OLIMEX/SOM/RK3188/RK3188-EVB/RK3188-EVB_Rev_C1.pdf

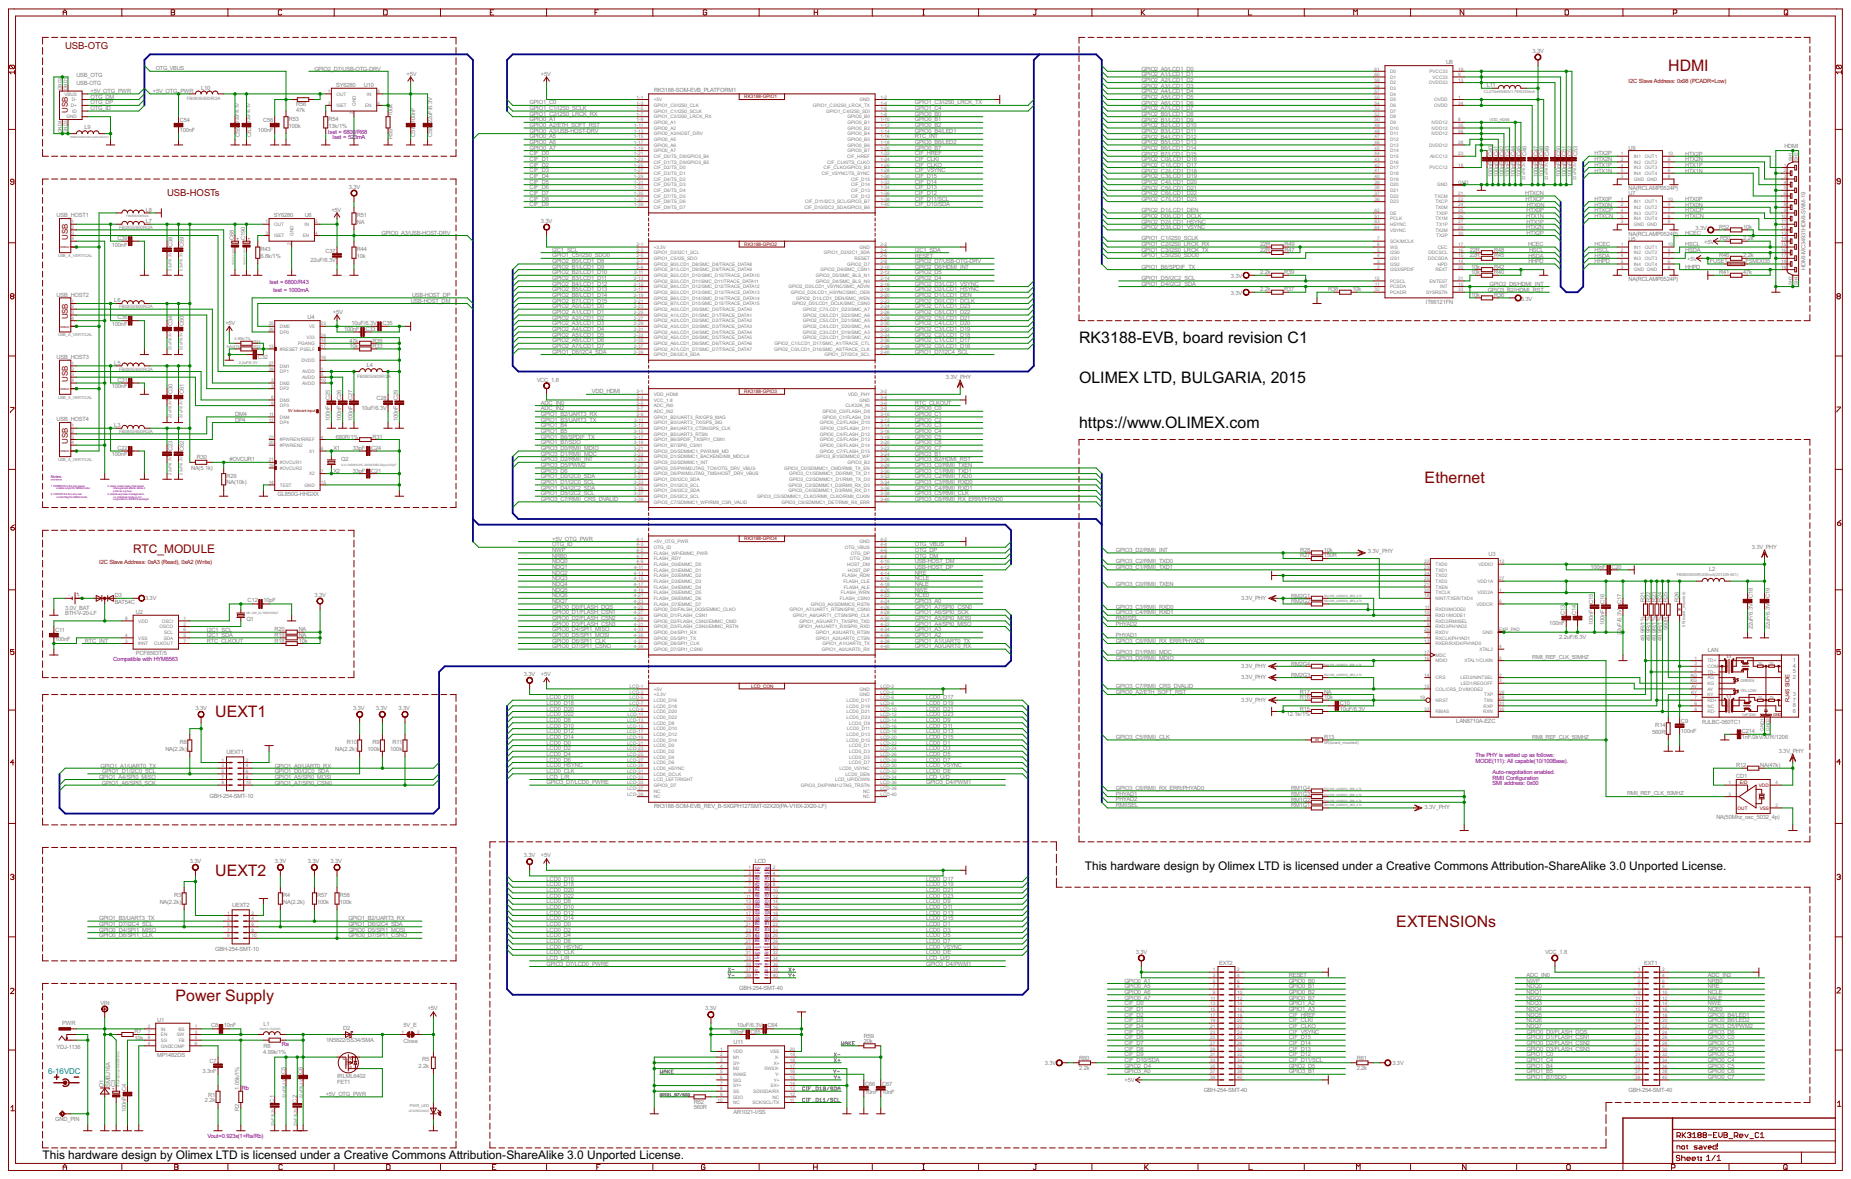
[picture p11: page 1]

I2C Slave Address: 0x98 (PCADR=Low)

NA(2 0uF/6.3V/tant)

RK3188-EVB, board revision C1 OLIMEX LTD, BULGARIA, 2015

https://www.OLIMEX.com

enable output forGANGmode; 1. PWREN1# is the onlypower- Notes:

i.e. individual mode is not supported on SSOP28 package!

I2C Slave Address: 0xA3 (Read), 0xA2 (Write)

The PHY is setted up as follows: MODE(111): All capable(10/100Base). Auto-negotiation enabled. RMII Configuration SMI address: 0x00

This hardware design by Olimex LTD is licensed under a Creative Commons Attribution-ShareAlike 3.0 Unported License.

GND_PIN
Vout=0.923x(1+Ra/Rb) This hardware design by Olimex LTD is licensed under a Creative Commons Attribution-ShareAlike 3.0 Unported License.
