OLIMEX/SOM/RK3188/RK3188-EVB/RK3188-EVB_Rev_C.pdf

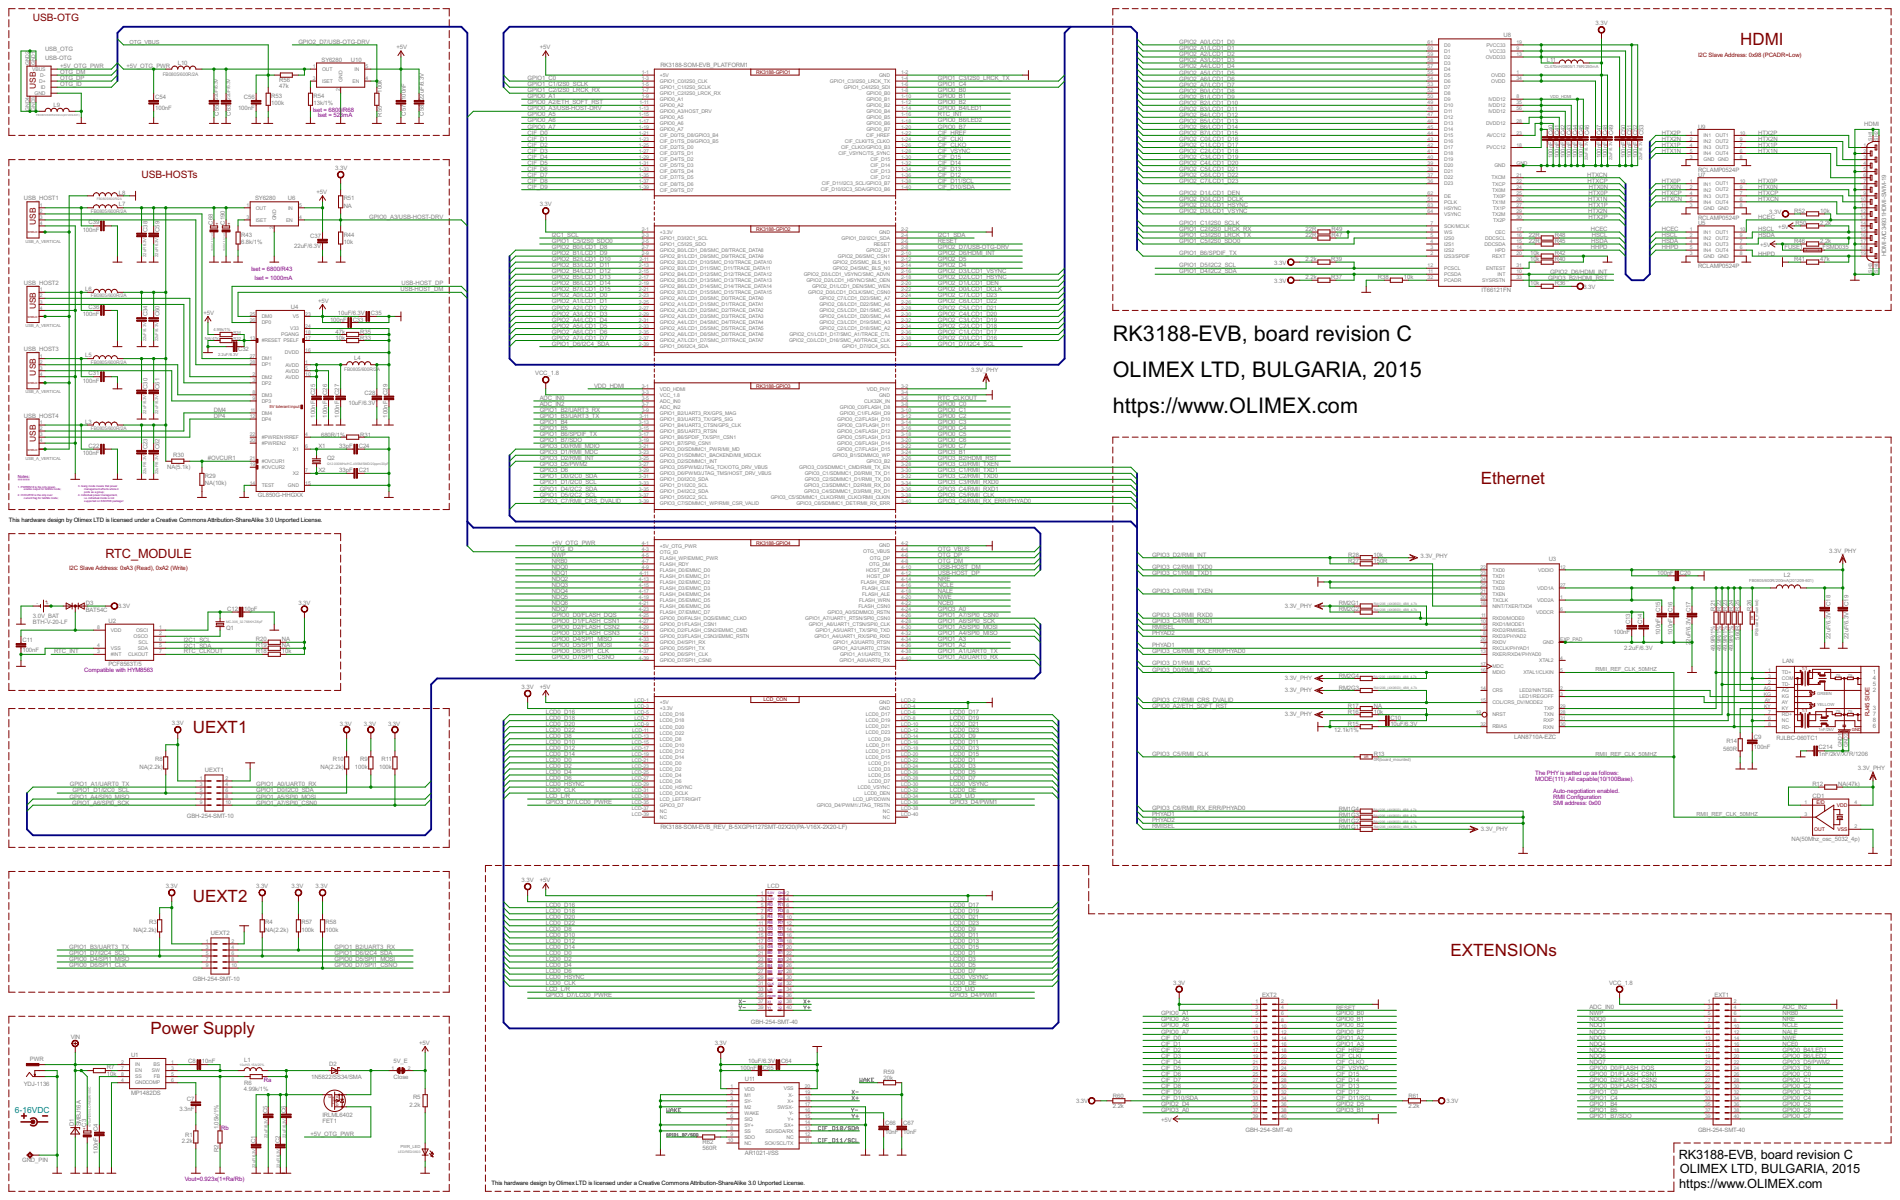
[picture p12: page 1]

I2C Slave Address: 0x98 (PCADR=Low)

NA(220uF/6.3V/tant)

https://www.OLIMEX.com

enable output for GANG mode; 1. PWREN1# is the only power- Notes:

i.e. individual mode is not supported on SSOP28 package!

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

I2C Slave Address: 0xA3 (Read), 0xA2 (Write)

USB-HOST_DP NRE NCLE NALE NWE NCE0 GPIO3_A0 GPIO1_A7/SPI0_CSN0 | GPIO3_C1/RMII_TXD1 GPIO3_C0/RMII_TXEN | 100nF | C20

KY 3 AG KG | COM NC AG KG AY KY | GREEN YELLOW

LCD0_D10 LCD-15 LCD0_D12 LCD-17 | LCD-16 LCD0_D11 LCD-18 LCD0_D13

LCD0_D2 LCD-23 LCD0_D4 LCD-25 | LCD-24 LCD0_D3 LCD-26 LCD0_D5

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

LCD0_D18 LCD0_D20 | 7 9 | 8 LCD0_D19 10 LCD0_D21

LCD0_D10 15 | 16 LCD0_D11

LCD0_D4 25 LCD0_D6 27 | 26 LCD0_D5 28 LCD0_D7

LCD0_HSYNC 29 LCD0_CLK 31 | HSYNC VSYNC CLK DE | 30 LCD0_VSYNC 32 LCD0_DE

GBH-254-SMT-40
RK3188-EVB, board revision C OLIMEX LTD, BULGARIA, 2015
