OLIMEX/SOM/A13/A13-SOM-LTE/A13-SOM-LTE_Rev_B.pdf

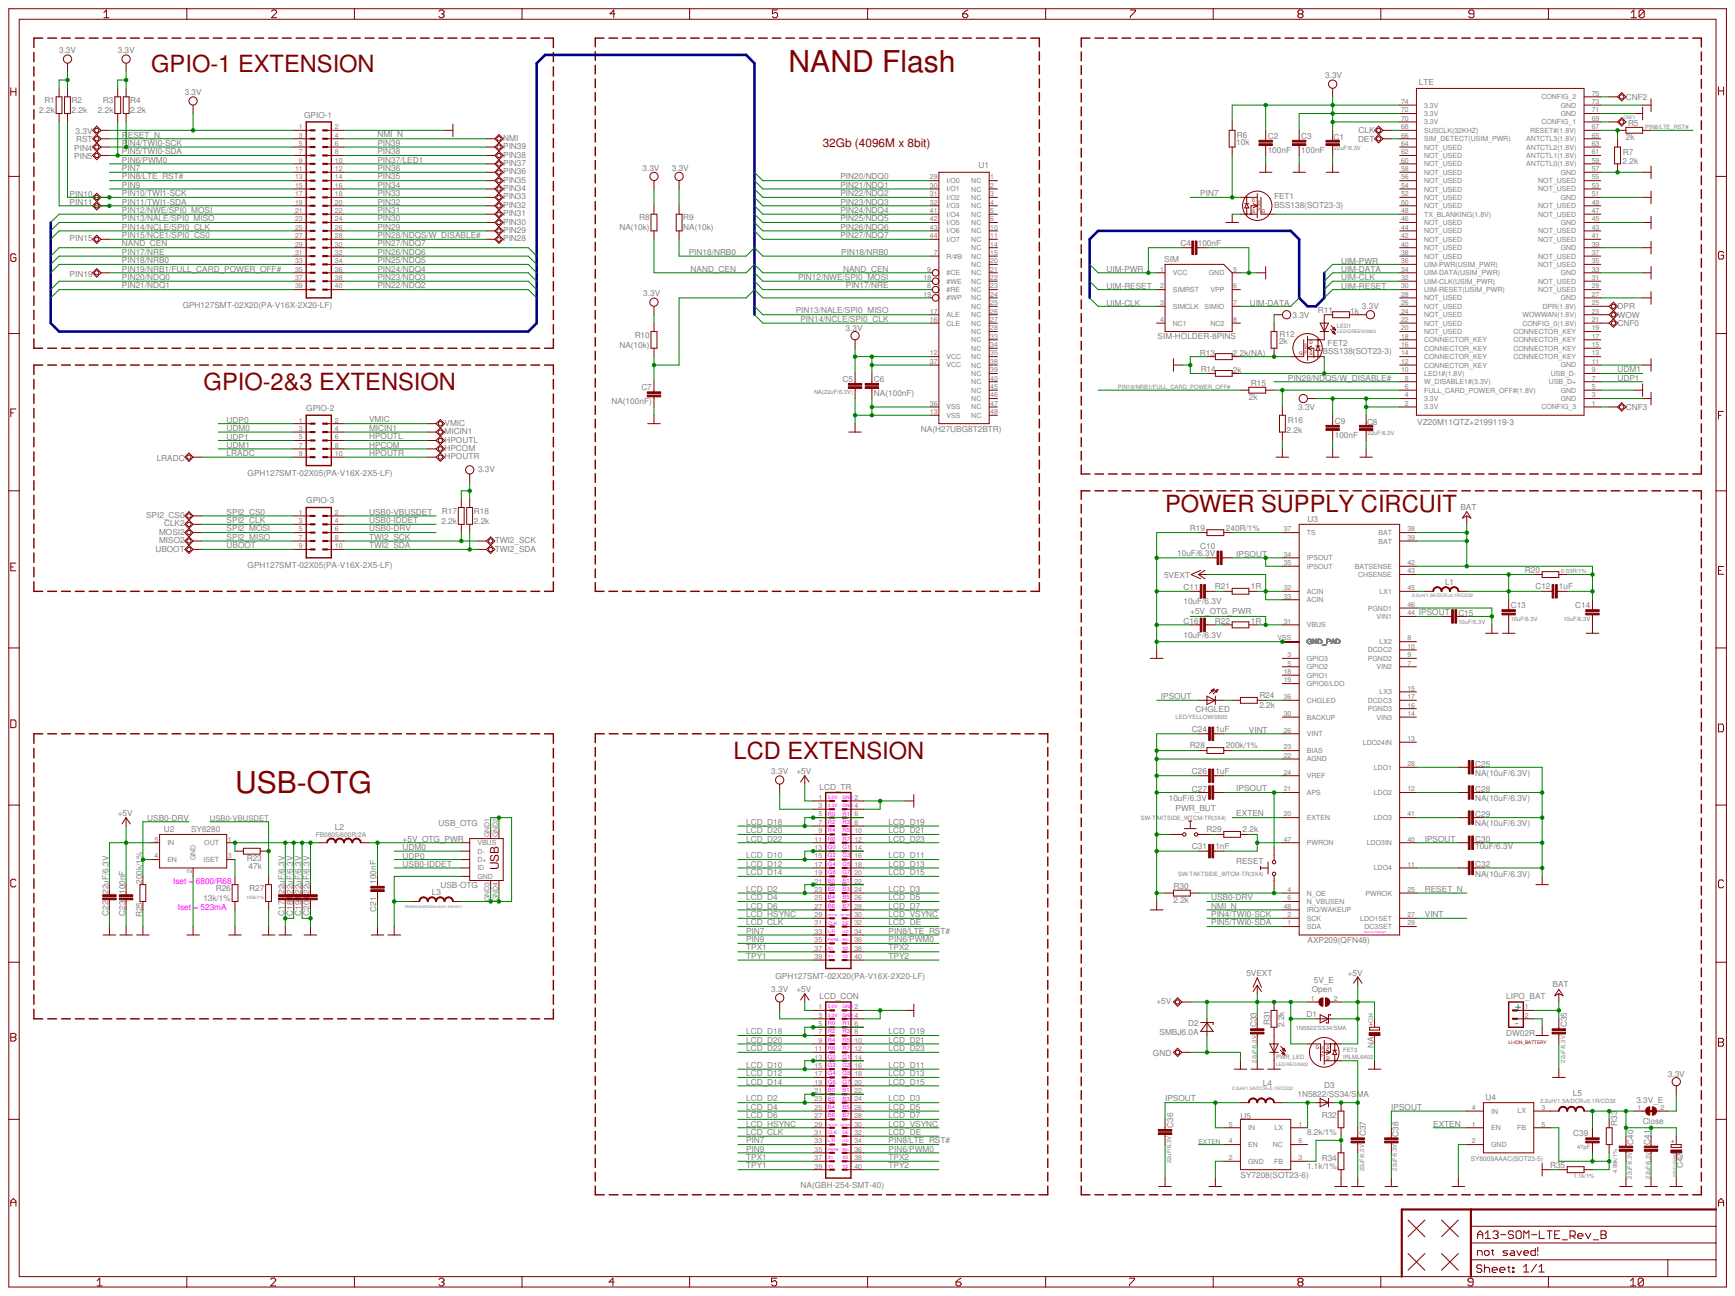
[picture p14: page 1]

PIN4/TWI0-SCK 5 | 6 PIN39 PIN38
