OLIMEX/SOM/A13/A13-SOM-WIFI/A13-SOM-WIFI_Rev_B.pdf

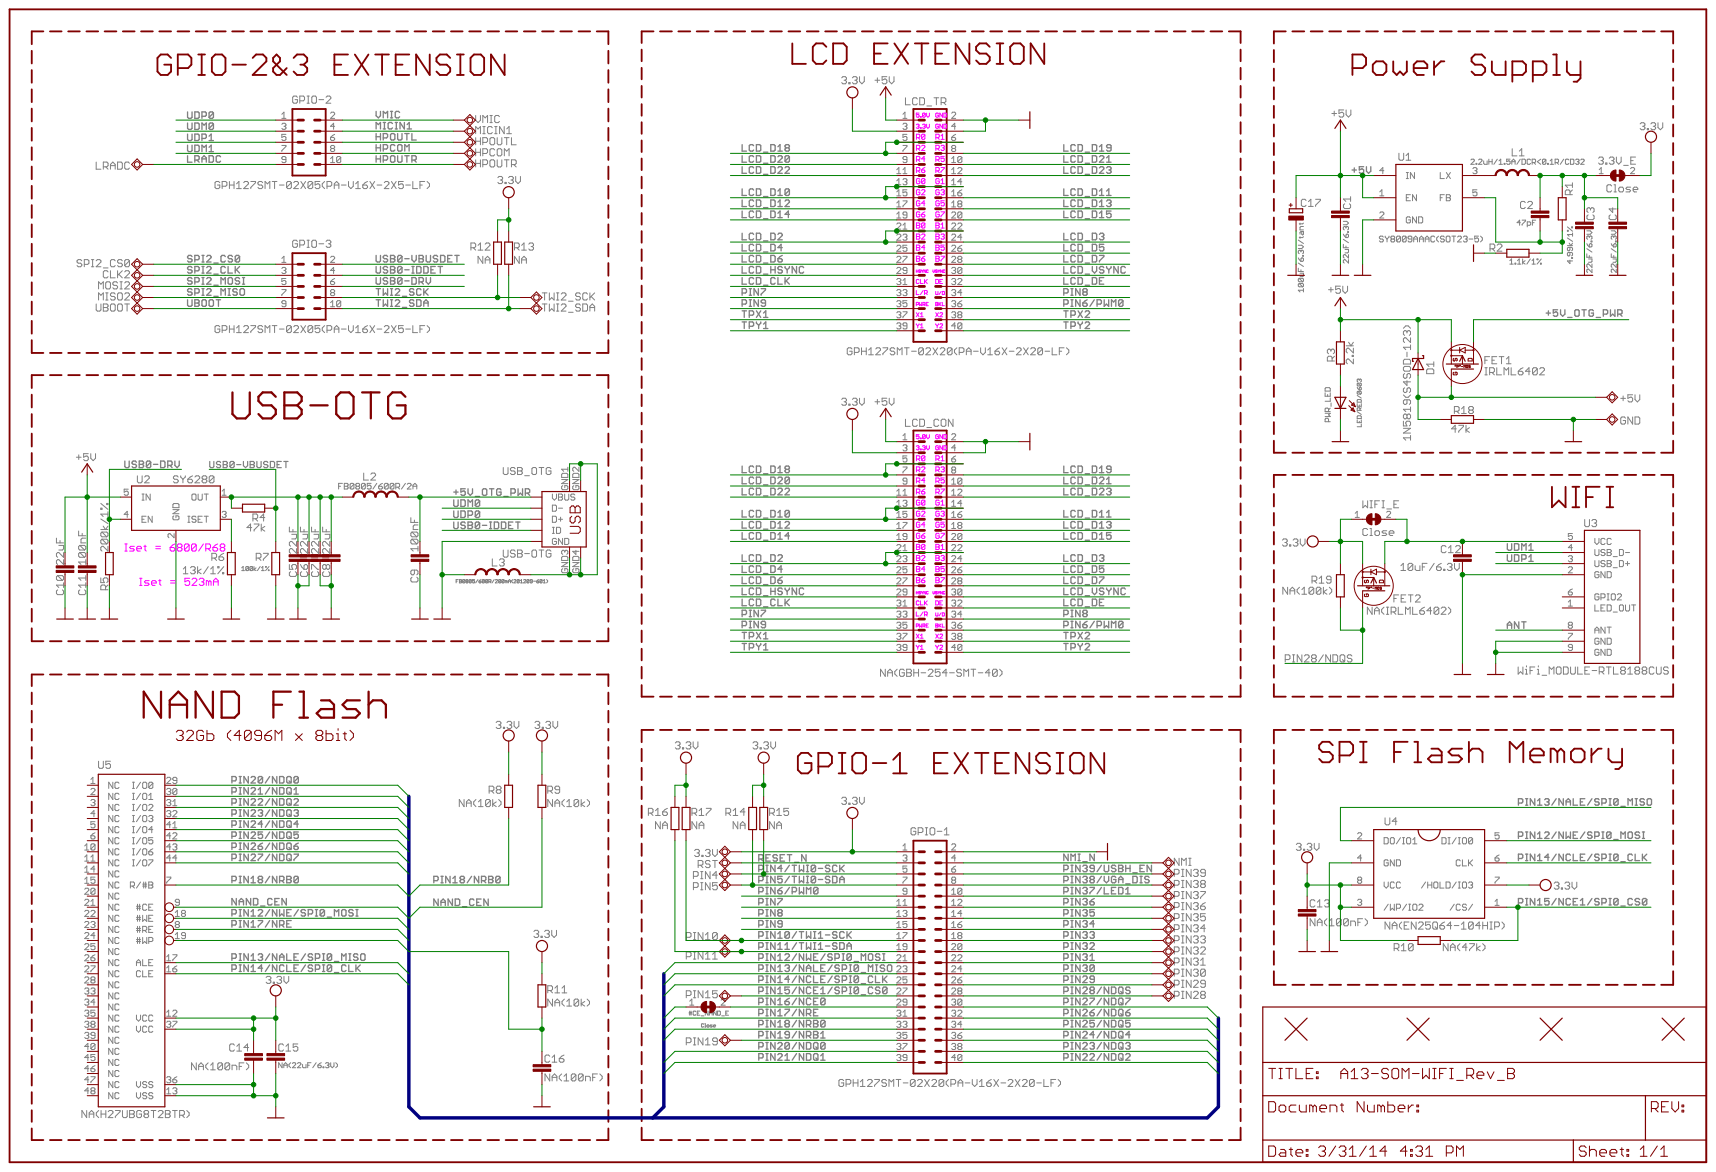
[picture p15: page 1]
