OLIMEX/SOM/A20/A20-SOM-EVB/A20-SOM-EVB_Rev_B.pdf

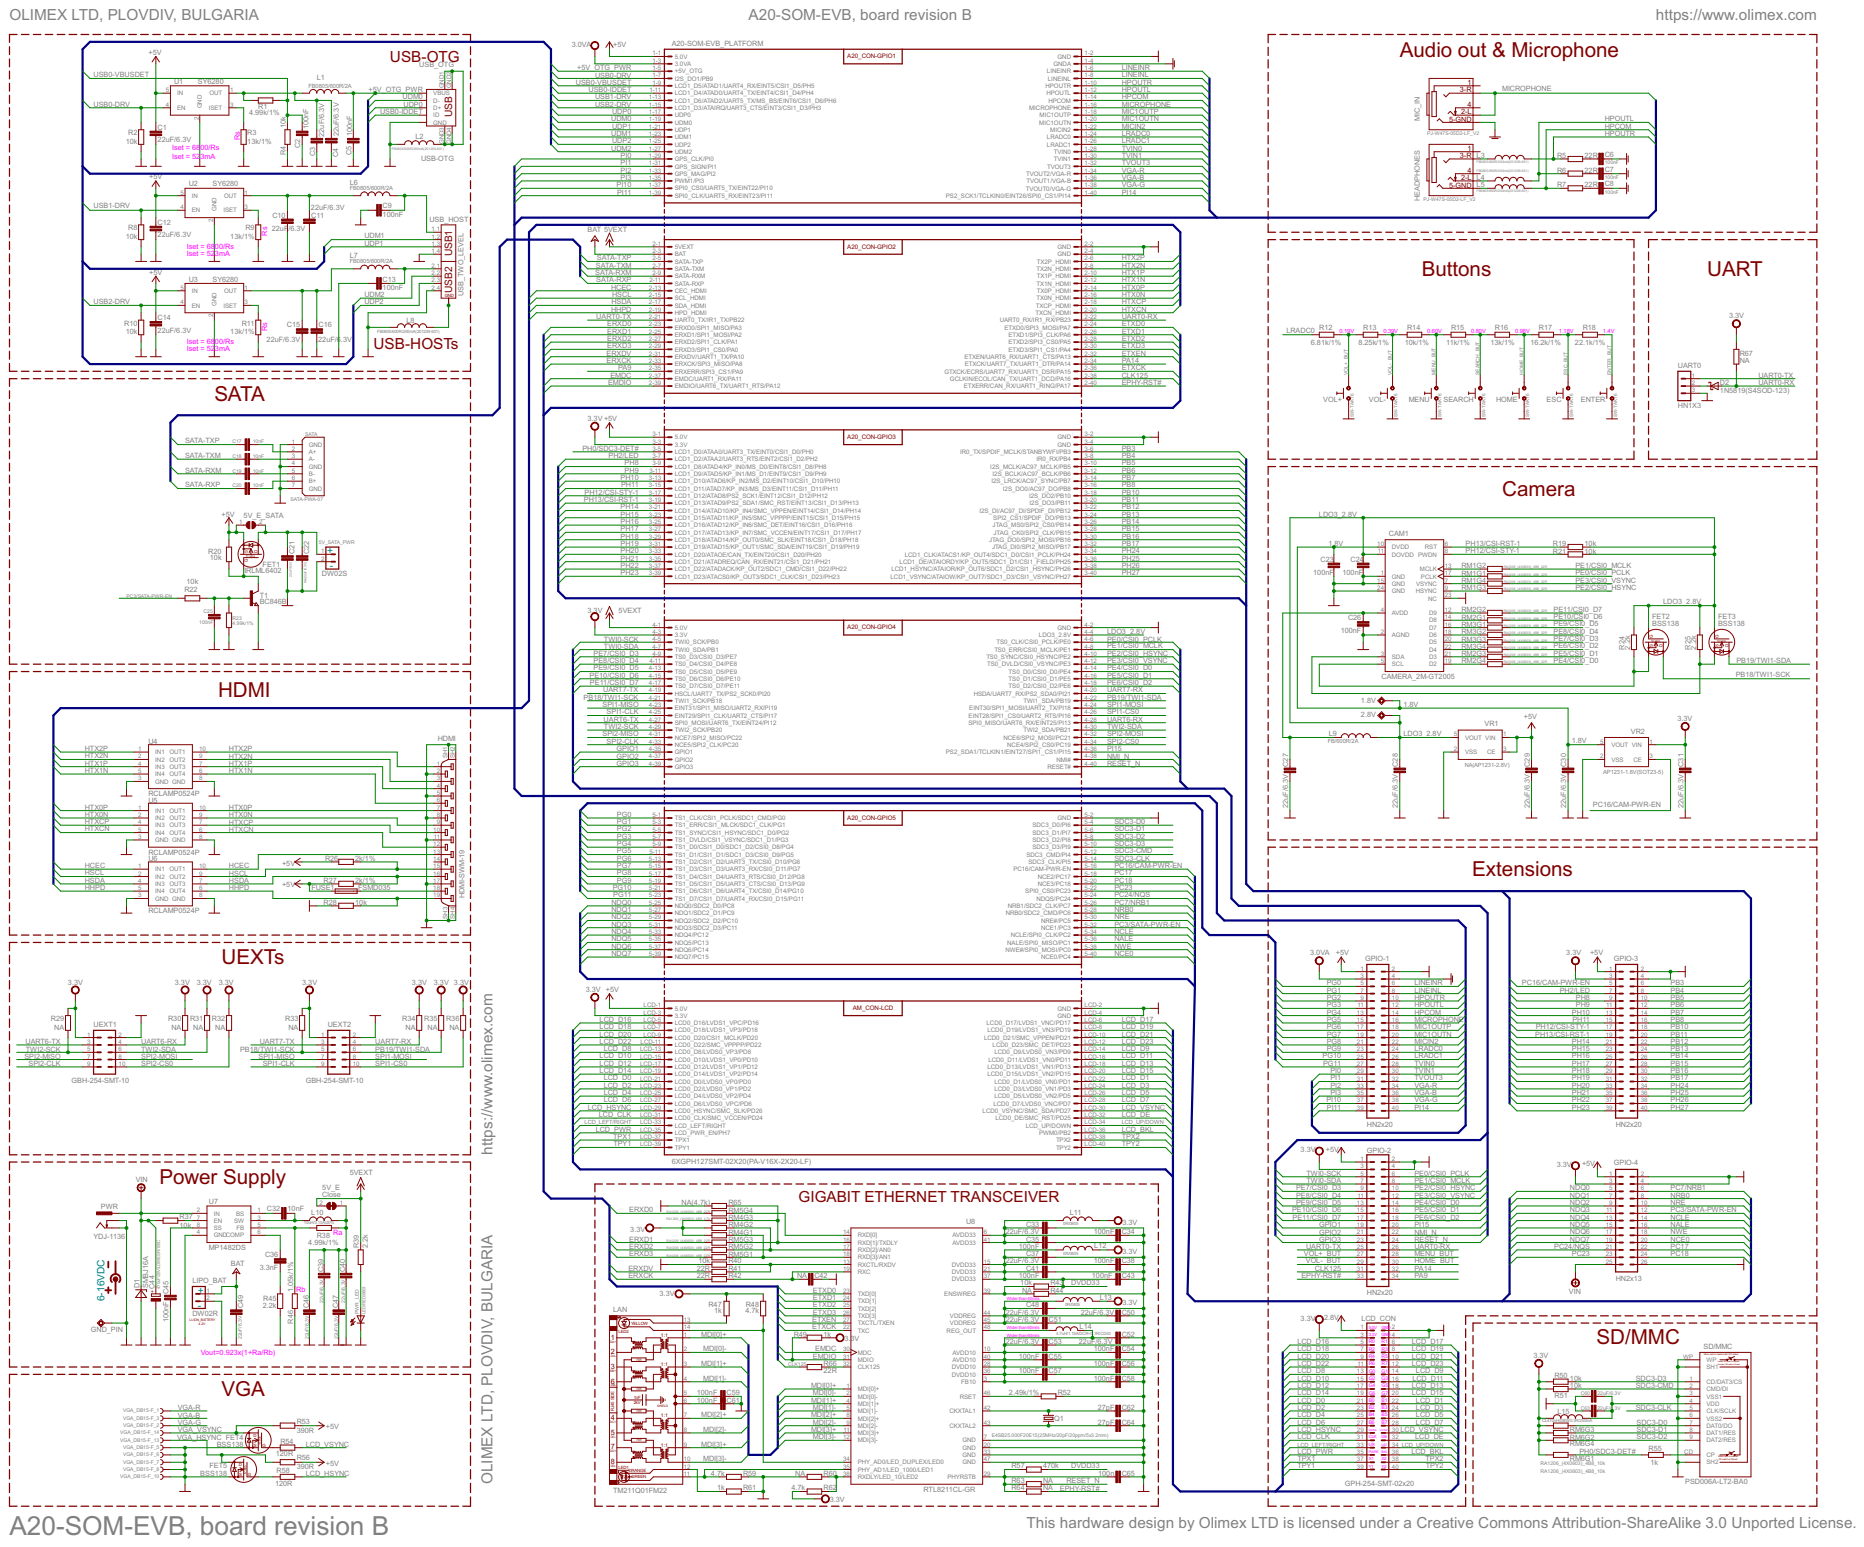
[picture p16: page 1]

OLIMEX LTD, PLOVDIV, BULGARIA

A20-SOM-EVB, board revision B

https://www.olimex.com

https:/ www.olimex.com

Wider than 40mils Wider than 60mils Wider than 60mils

When card is inserted with WP status: Locked, WP switch isOpened Unlocked, WP switch isClosed

When card is inserted, CP switch is Closed
