OLIMEX/SOM/A20/A20-SOM-EVB/A20-SOM-EVB_Rev_C.pdf

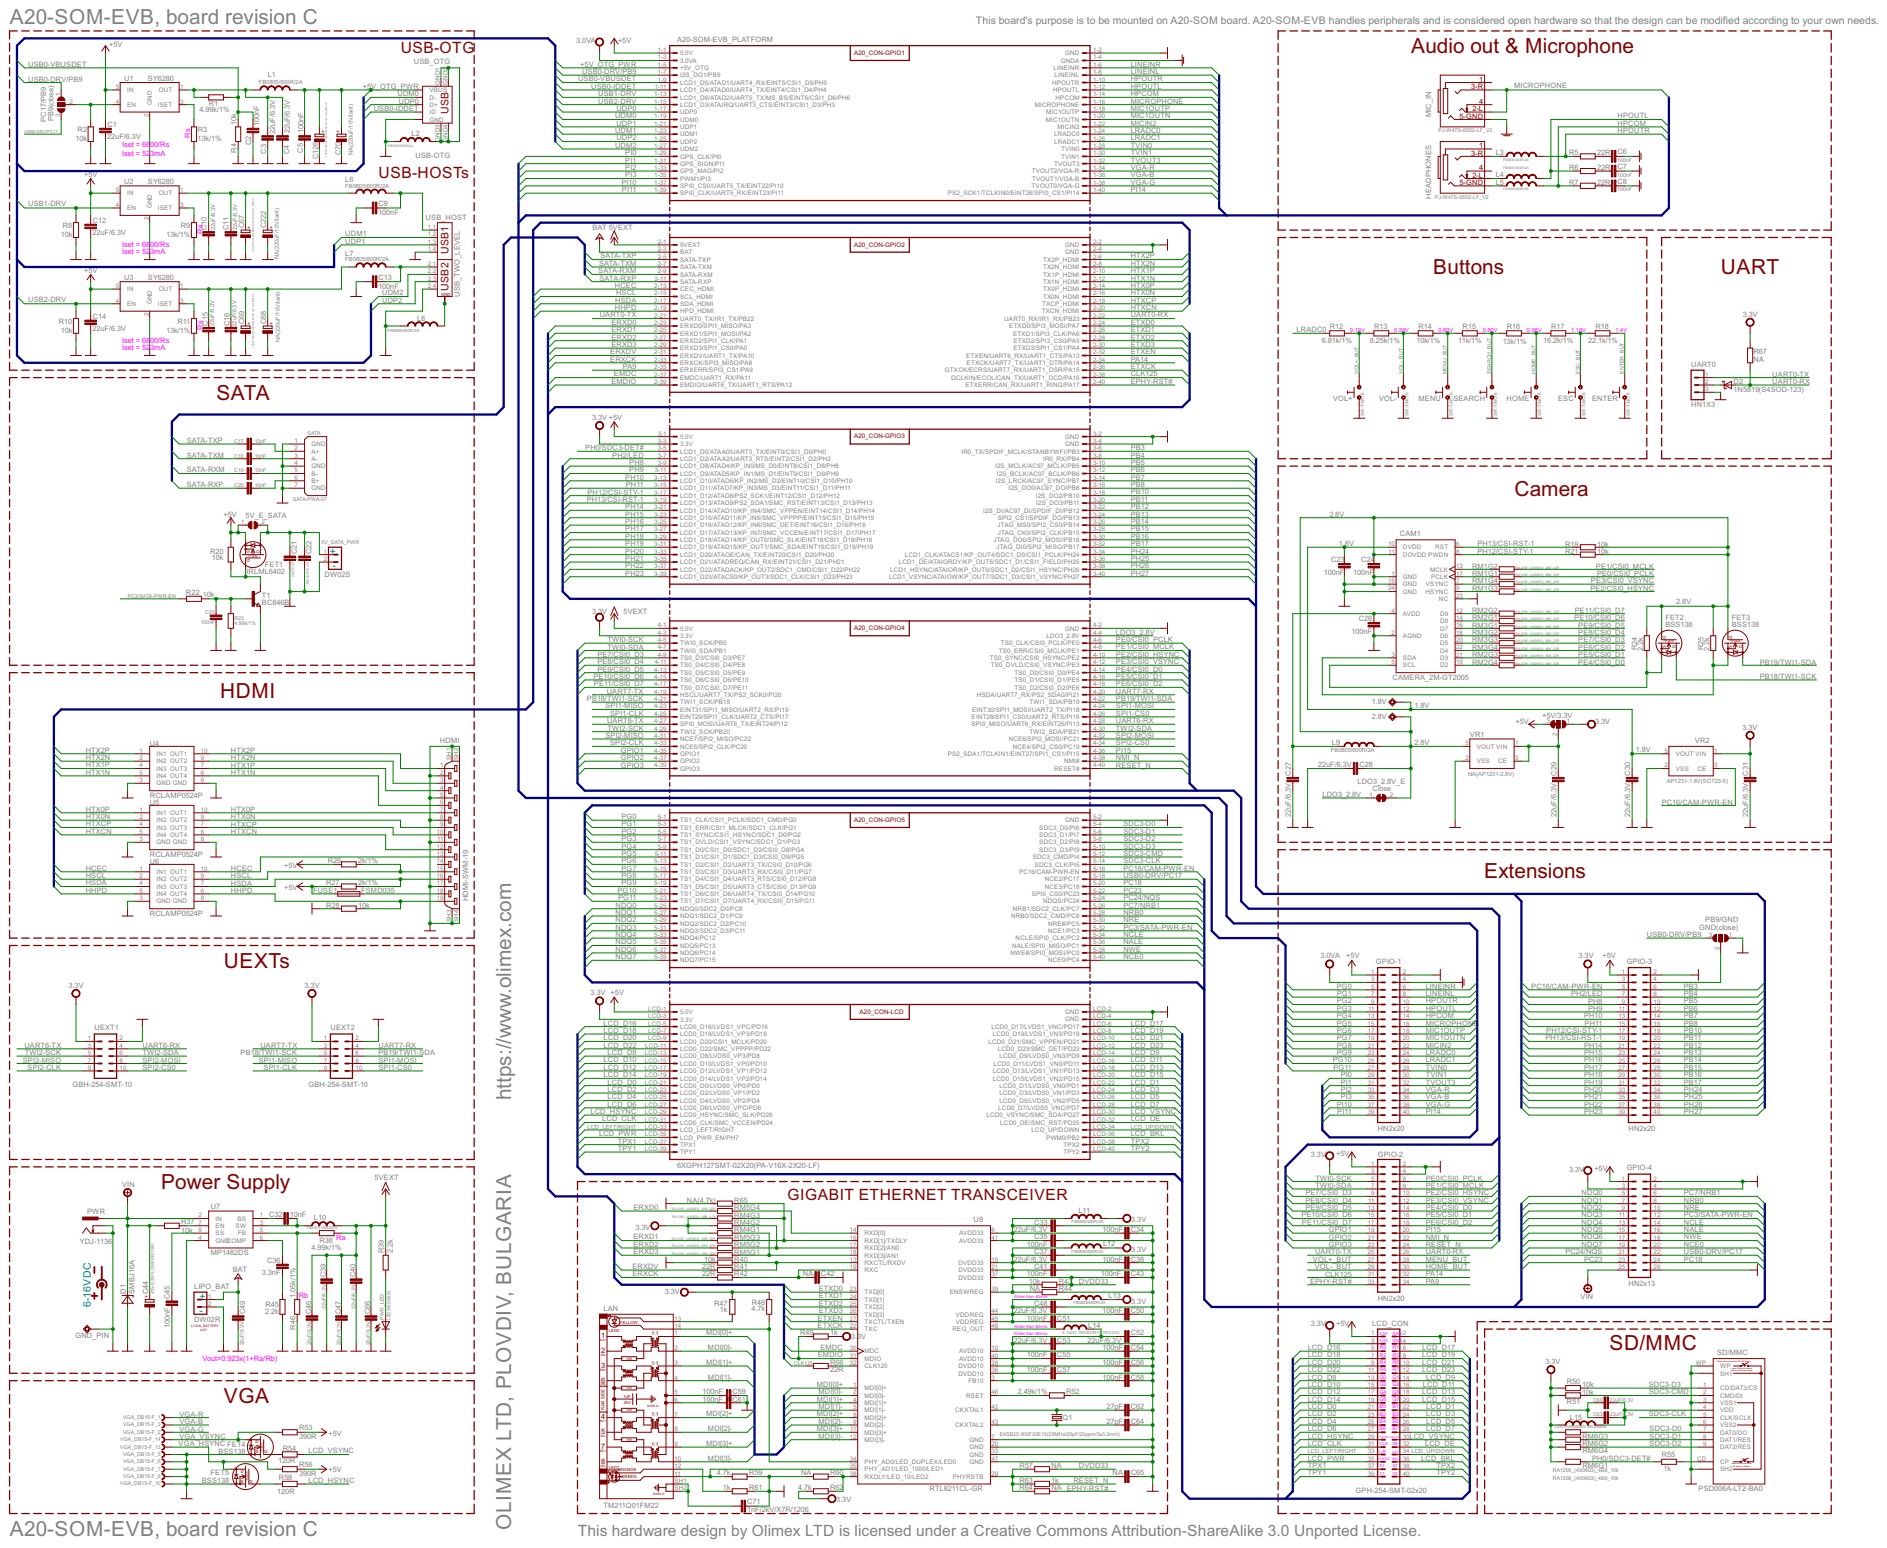
[picture p17: page 1]

A20-SOM-EVB, board revision C

This board's purpose is to be mounted on A20-SOM board. A20-SOM-EVB handles peripherals and is considered open hardware so that the design can be modified according to your own needs.

NA(220uF/10V/tant)

Wider than 40mils Wider than 60mils Wider than 60mils

When card is inserted with WP status: Locked, WPswitch is Opened Unlocked, WPswitch is Closed

When card is inserted, CP switch is Closed

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
