OLIMEX/SOM/A20/A20-SOM/A20-SOM_board_rev_B.pdf

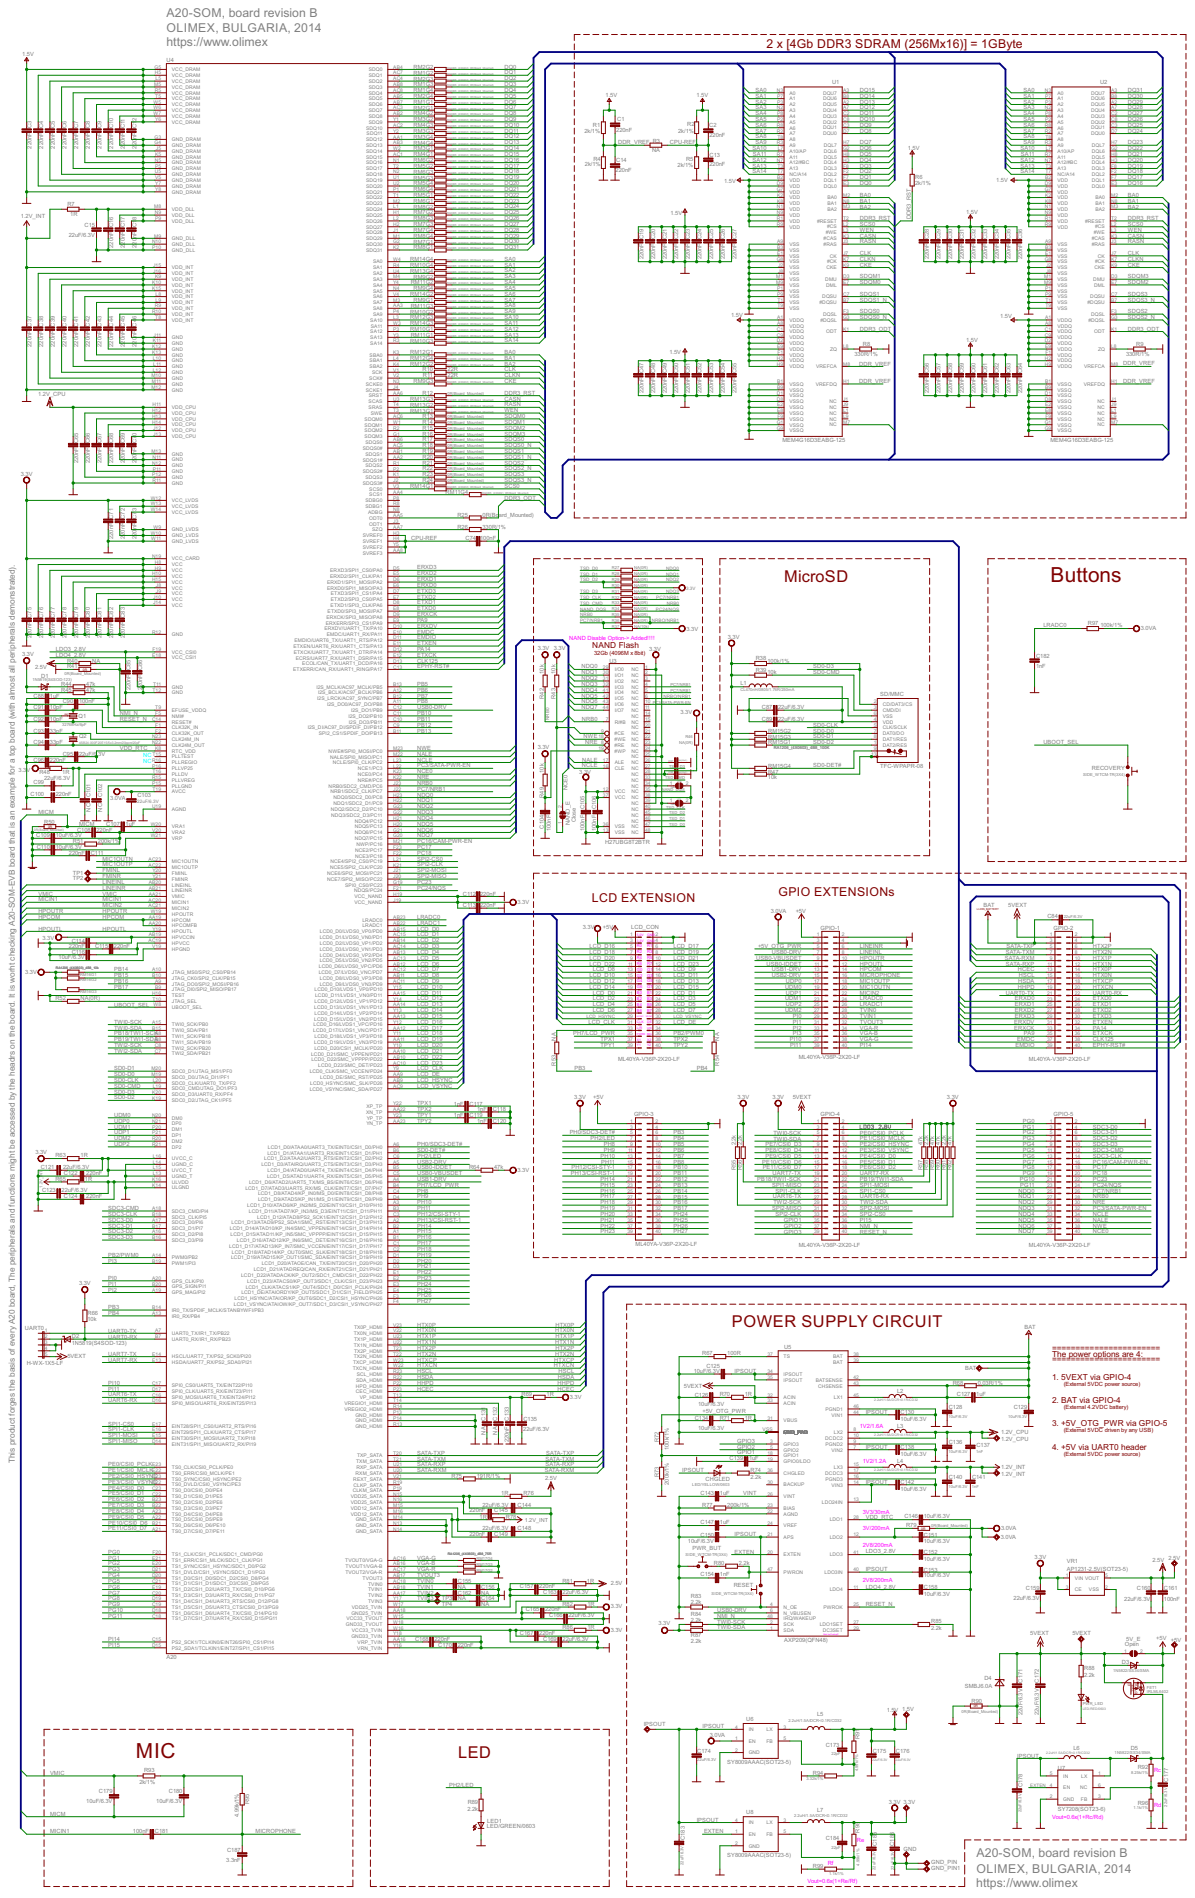
[picture p18: page 1]

A20-SOM, board revision B OLIMEX, BULGARIA, 2014

This product forges the basis of every A20 board, The peripherals and functions might be accessed by the headrs on the board. It is worht checking A20-SOM-EVB board that is an example for a top board (with almost all peripherals demonstrated).

GPIO EXTENSIONs LCD EXTENSION

PH12/CSI-STY-1
PH13/CSI-RST-1

The power options are 4: 1. 5VEXT via GPIO-4

(External 5VDC power source)
2. BAT via GPIO-4
(External 4.2VDC battery)
3. +5V_OTG_PWR via GPIO-5
(External 5VDC driven by any USB)

Rc Rd Vout=0.6x(1+Rc/Rd) Re Rf Vout=0.6x(1+Re/Rf)
