OLIMEX/SOM/A13/A13-SOM/A13-SOM512_Rev_D.pdf

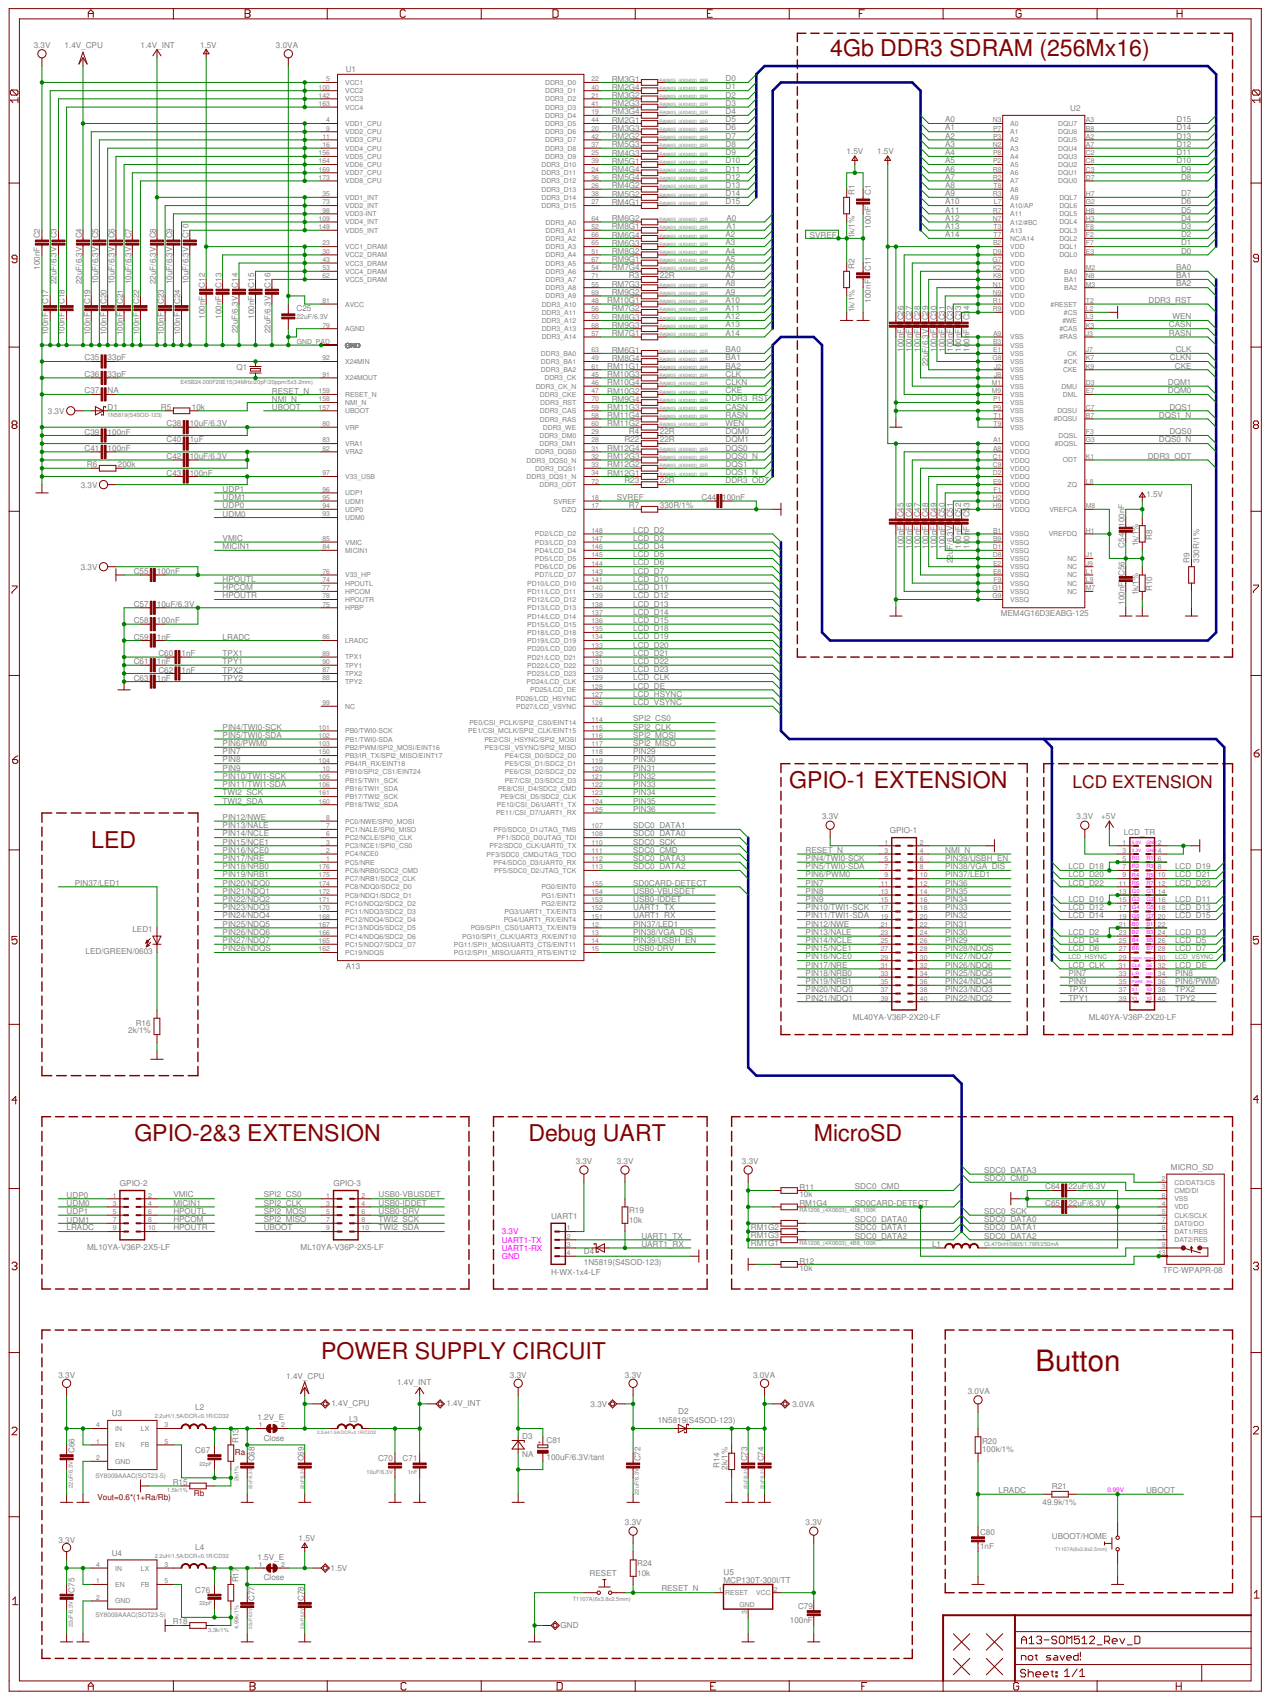
[picture p19: page 1]

142 | RM2G1 RM2G2 RM2G3 RM2G4 RM3G1 RM3G2 RM3G3 RM3G4 40 DDR3_D3
100 | 21 DDR3_D0

100nF | 83 | 29 R4
100nF | | 31 DDR3_DQS0_N

1uF | 28 DDR3_DM0

10uF/6.3V 97 | 32 DDR3_DQS1

1nF | TPY1 90 | LCD_D22
1nF TPX2 | 130 PD22/LCD_D22 LCD_D23 129 PD23/LCD_D23
1nF | TPY2 | LCD_CLK

12 PIN36 | LCD_D22 11 | 12 LCD_D23
