OLIMEX/SOM/A20/A20-SOM/A20-SOM_board_rev_E.pdf

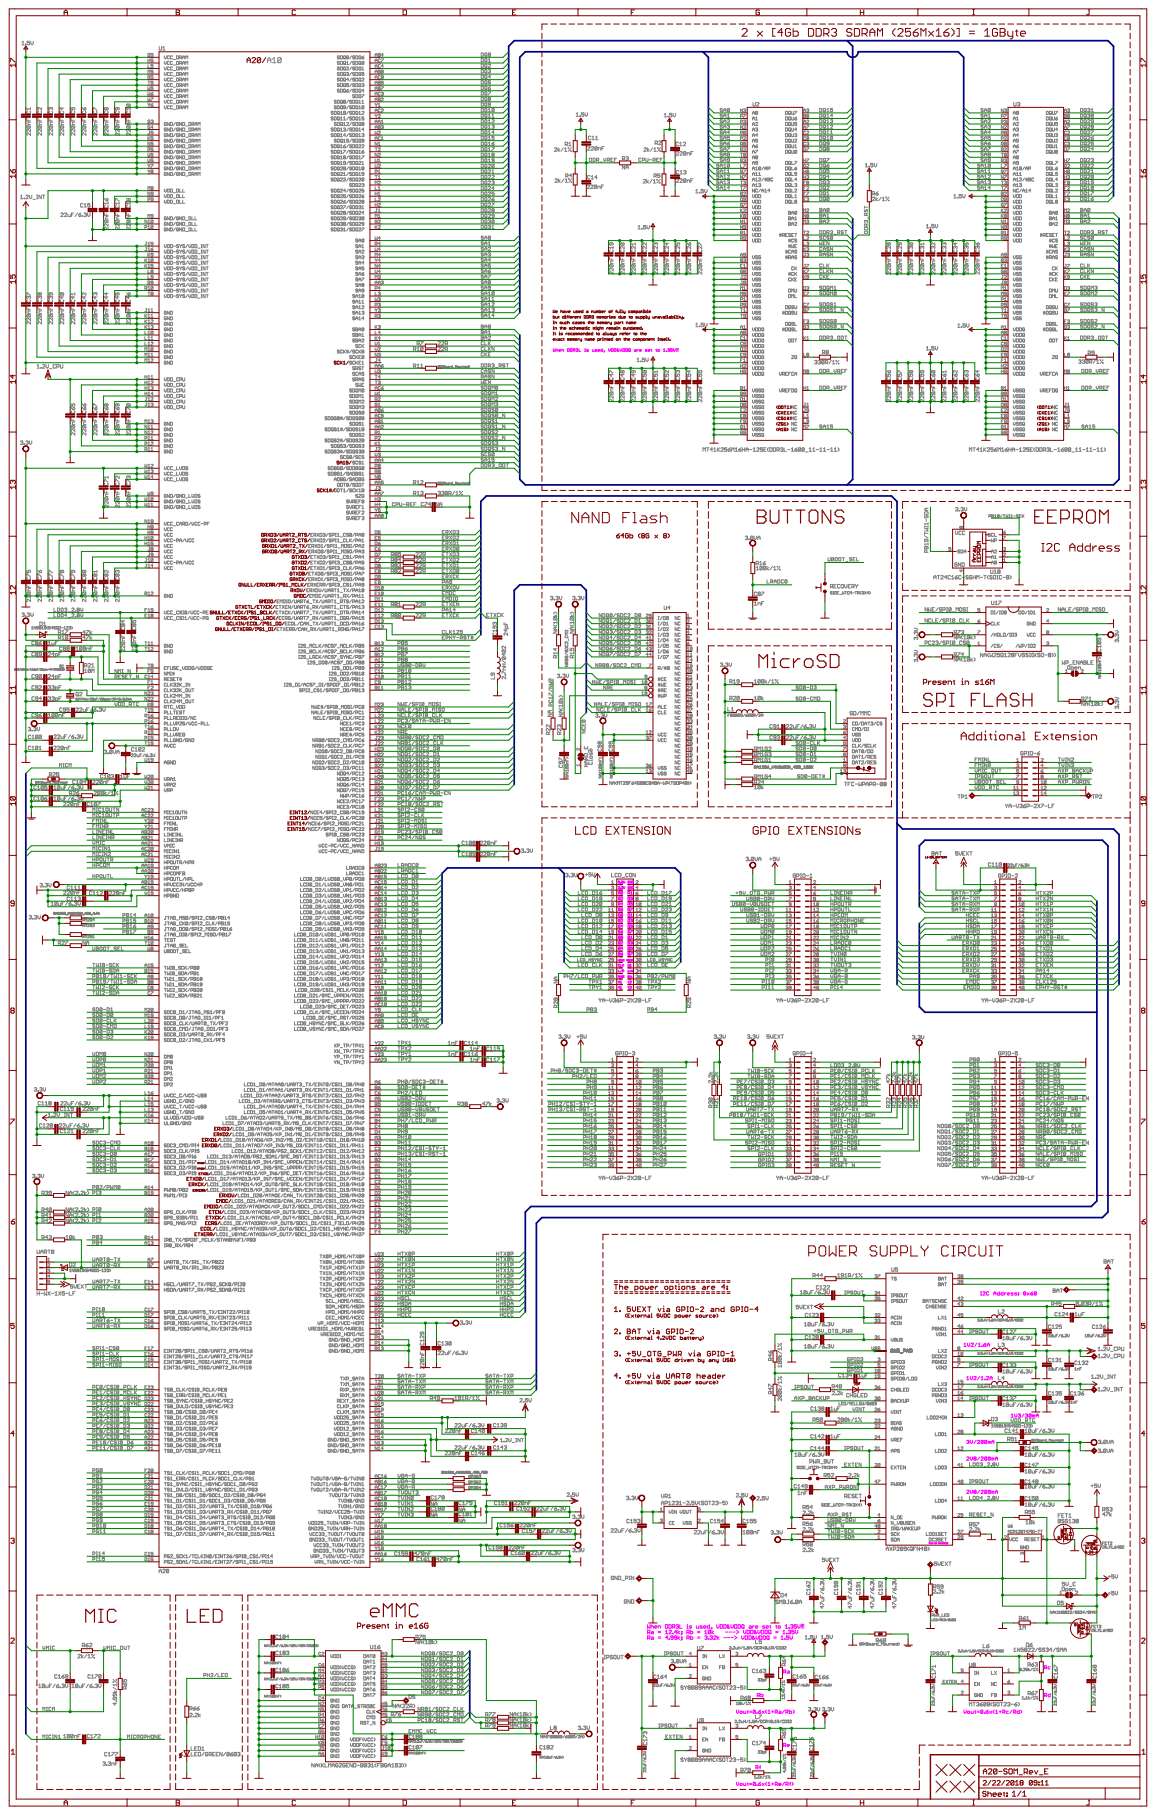
[picture p20: page 1]
